alvarop/reloj/pictures/IMG_2830.jpg

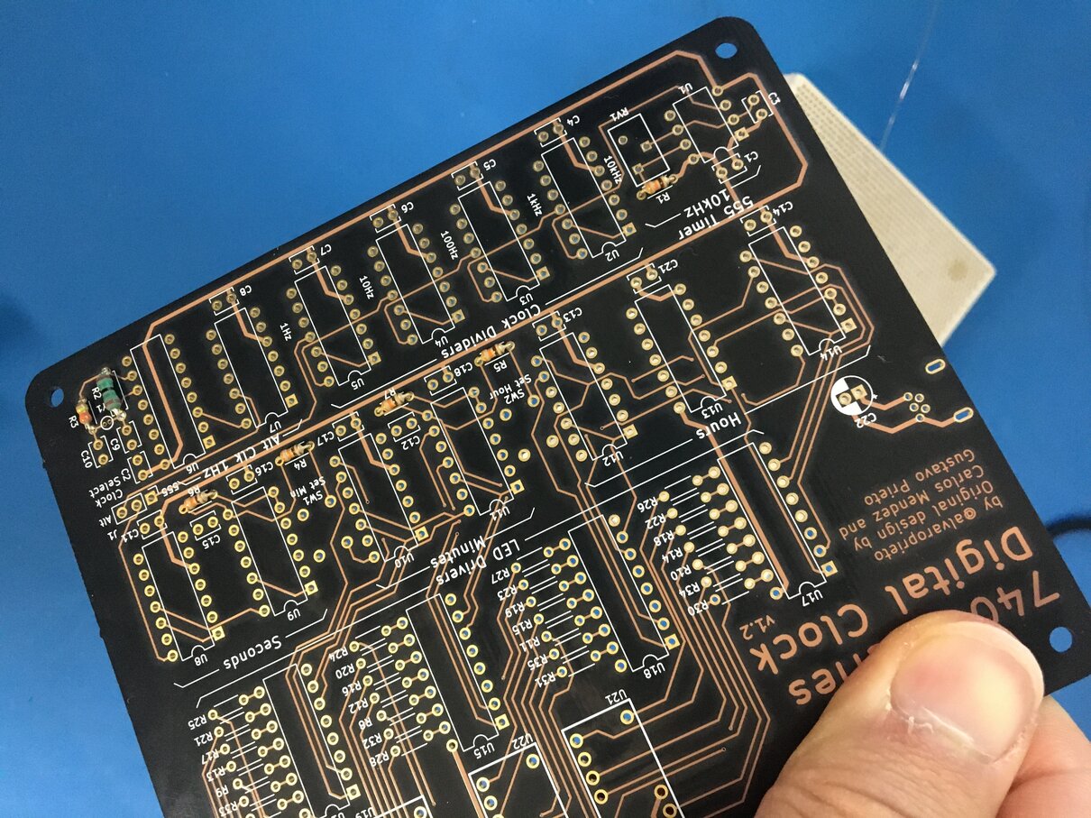
pictures/IMG_2830.jpg
