alvarop/reloj/pictures/IMG_2831.jpg

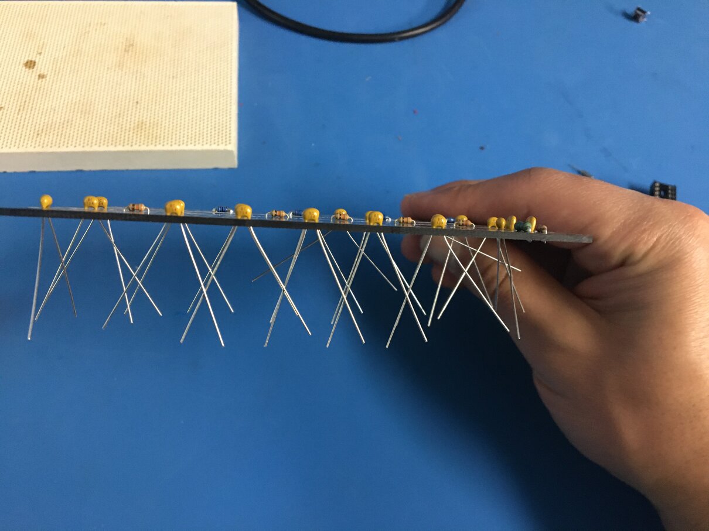
pictures/IMG_2831.jpg
