alvarop/reloj/pictures/IMG_2861.jpg

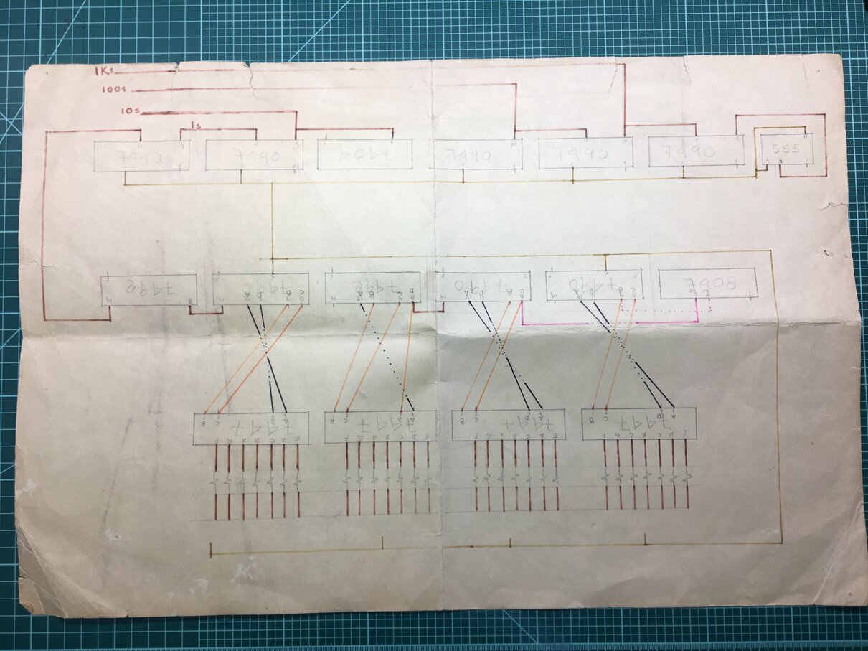
pictures/IMG_2861.jpg
