alvarop/reloj/pictures/IMG_2862.jpg

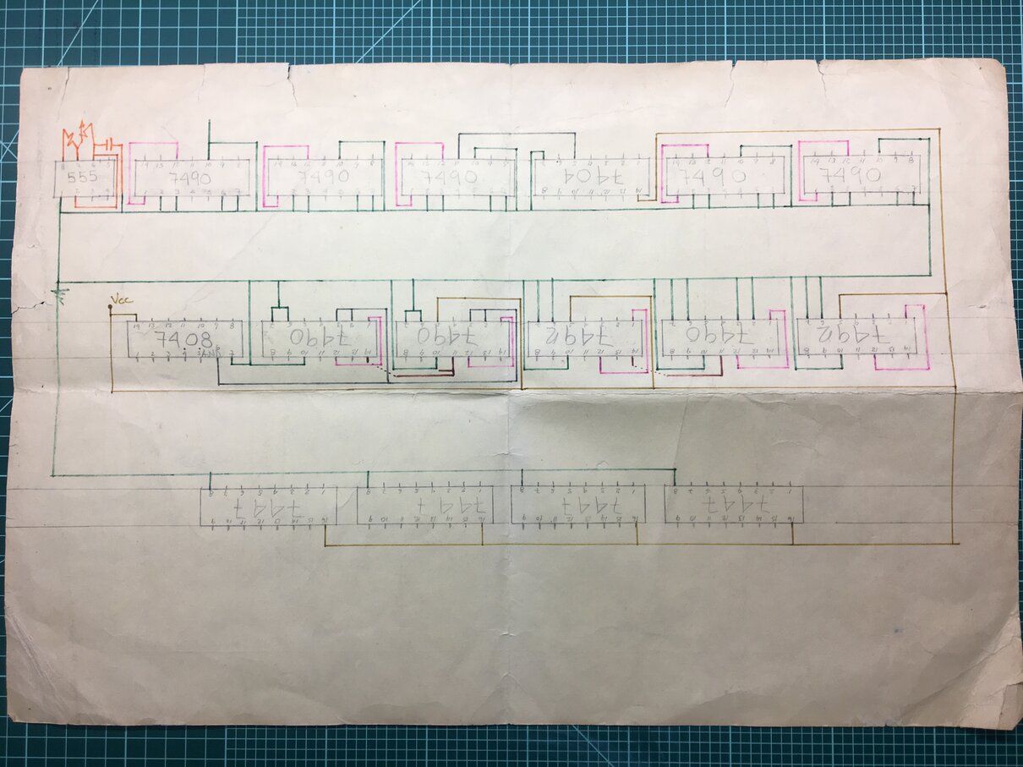
pictures/IMG_2862.jpg
