alvarop/reloj/pictures/IMG_6954.jpg

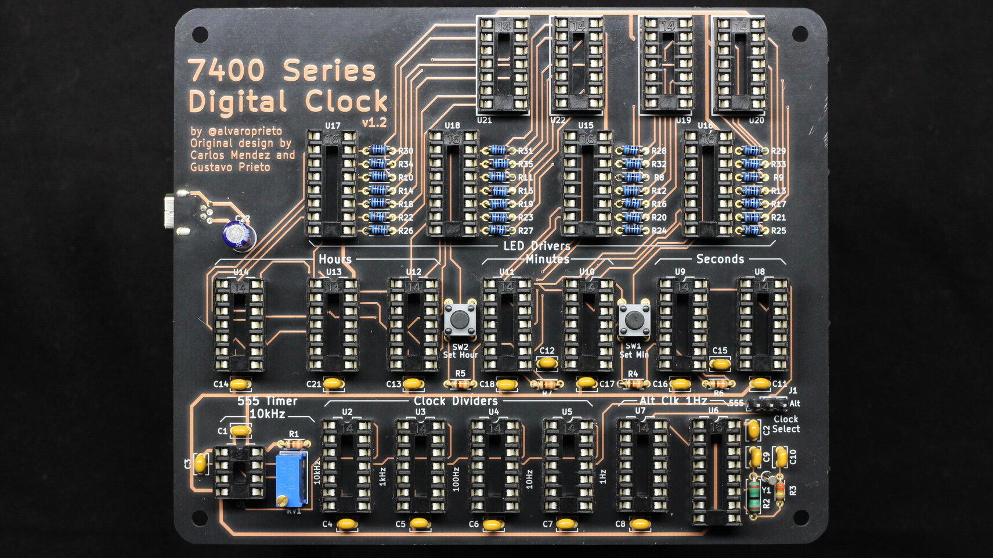
pictures/IMG_6954.jpg
