alvarop/reloj/pictures/IMG_6955.jpg

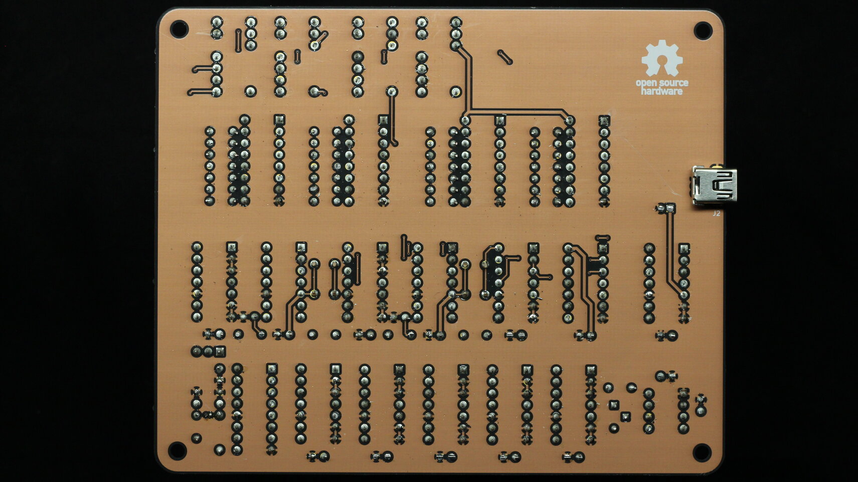
pictures/IMG_6955.jpg
