alvarop/reloj/pictures/IMG_6957.jpg

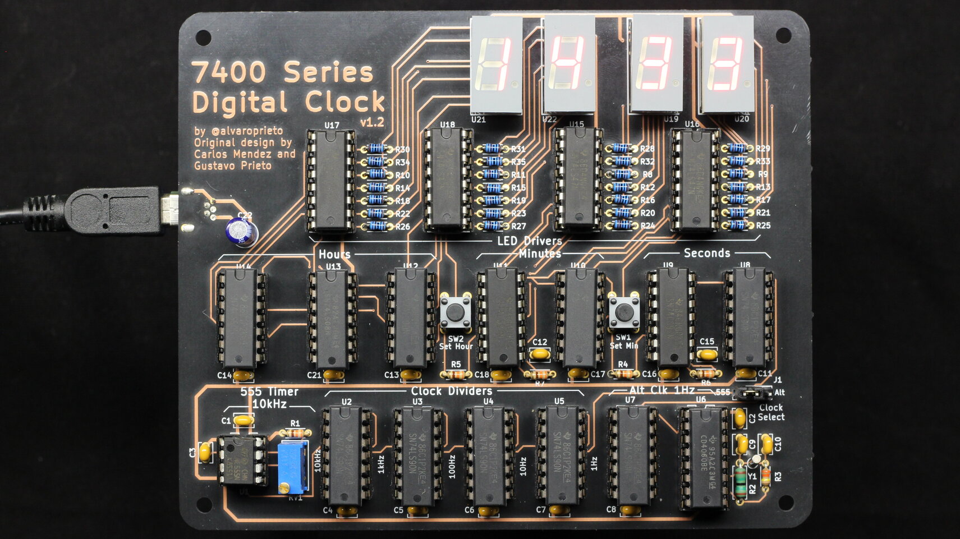
pictures/IMG_6957.jpg
