alvarop/reloj/pictures/IMG_6958.jpg

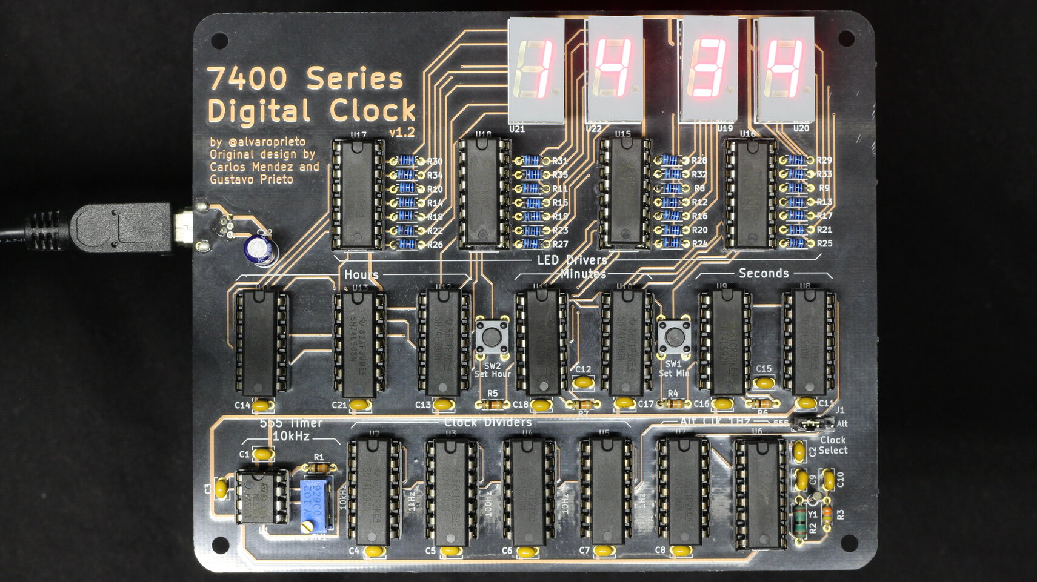
pictures/IMG_6958.jpg
