alvarop/reloj/pictures/IMG_6959.jpg

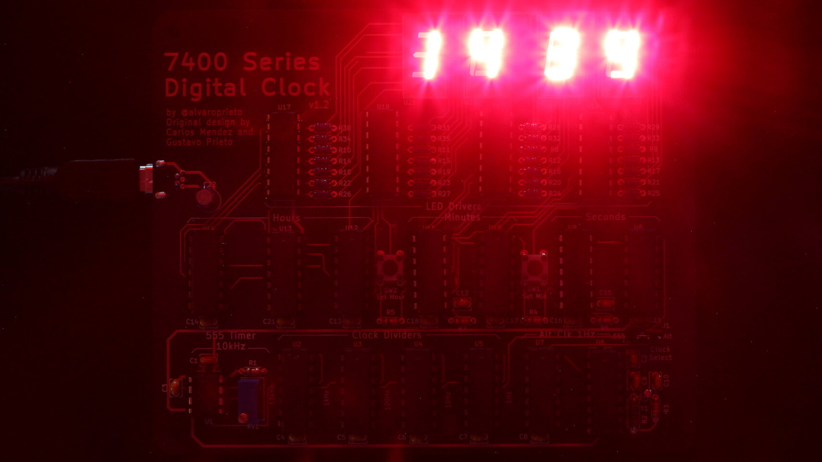
pictures/IMG_6959.jpg
